cjakma/wood-case-keyboard/pics/IMG_2515.JPG

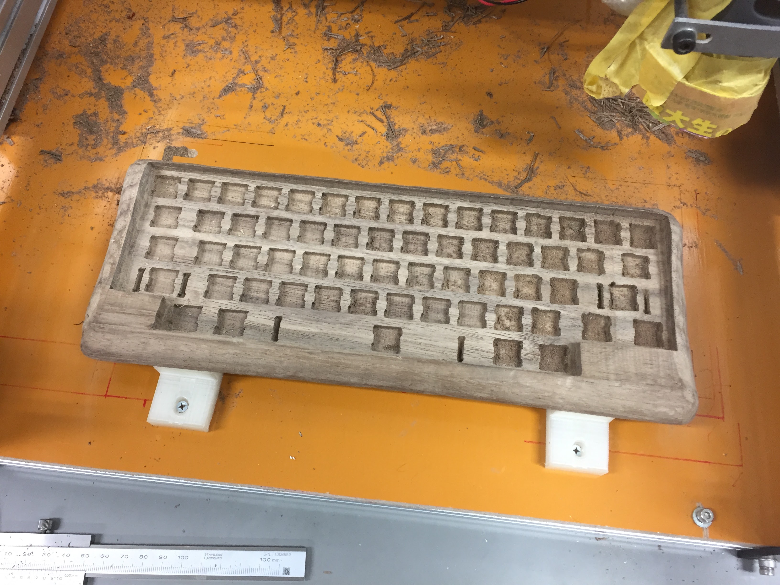
pics/IMG_2515.JPG
