cjakma/wood-case-keyboard/pics/IMG_2516.JPG

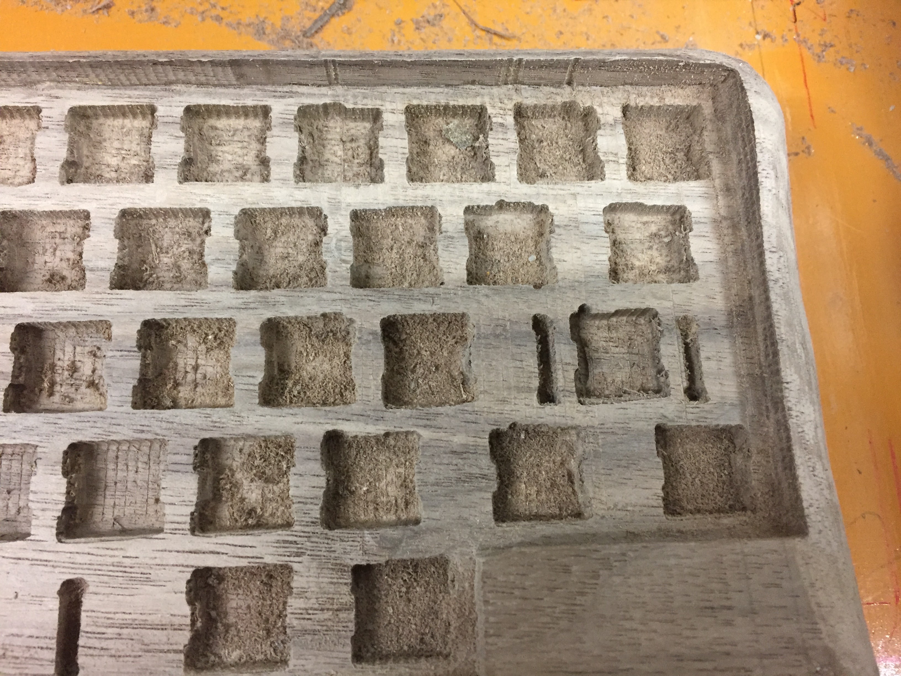
pics/IMG_2516.JPG
