cjakma/wood-case-keyboard/pics/IMG_2567.JPG

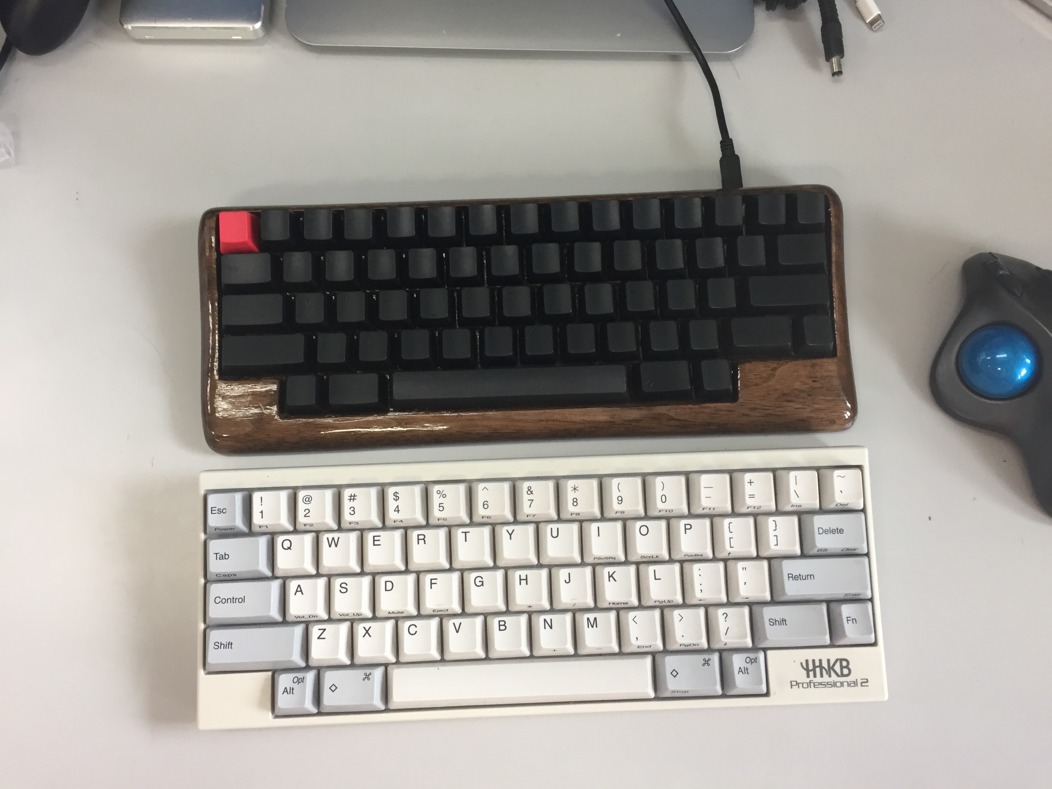
pics/IMG_2567.JPG
