cjakma/wood-case-keyboard/pics/IMG_2568.JPG

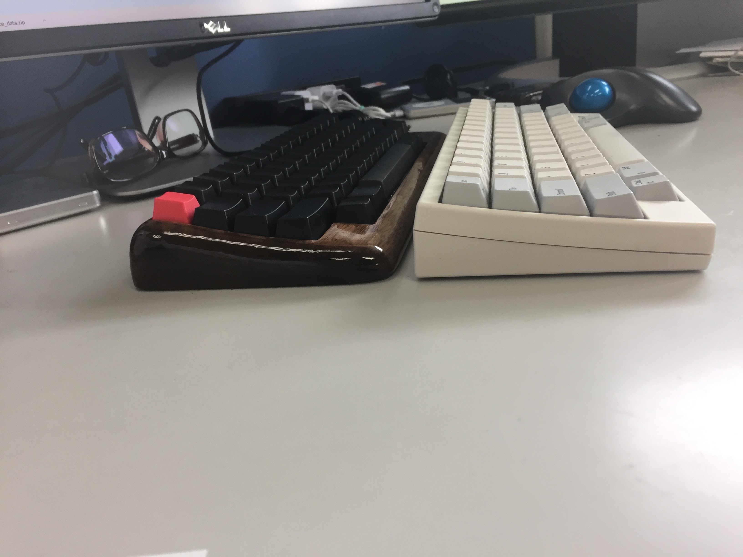
pics/IMG_2568.JPG
