cjakma/wood-case-keyboard/pics/IMG_2570.JPG

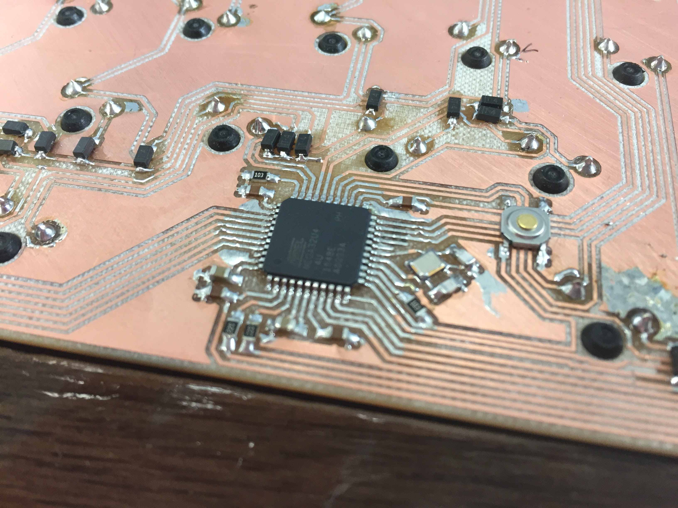
pics/IMG_2570.JPG
