cjakma/wood-case-keyboard/model/bottom_cutout.scad

use <scad-utils/morphology.scad>
include <common.scad>


invert_2D() bottom_cutout_2D();

/* bottom_cutout(); */
module bottom_cutout_2D()
{
    outset(r=0.5)
    square(plate_size);
}

module bottom_cutout()
{
    difference()
    {
        cube([plate_size()[0], plate_size()[1], block_height()]);

        translate((block_height()-lip_depth()-3.6)*z())
        linear_extrude(height=lip_depth()+3.6+0.1)
        bottom_cutout_2D();
    }
}
