cjakma/wood-case-keyboard/model/common.scad

include <params.scad>

inch = 25.4;
unit = 19.05;
x = [1, 0, 0];
y = [0, 1, 0];
z = [0, 0, 1];

// margin as 2D vector, to be added outside of the keyboard 
margin = [3, 2];

// tilt angle of the keyboard in degree unit
tilt = 10;

// ront_height height of the keyboard at front side. overall height will be
// calculated based on front_height and tilt_angle. make sure that there is
// enough room for PCB to be placed under the keyboard.
front_height = 14;

// roundnessness radius at side
roundness = 10;

// size of material to carve
block_size = [330, 130, 34];

// roundness of top of case
R = 400;

// maximum distance from top of your keyboard to switch mount surface.
lip_depth = 7.5;

// following are calcualted parameters
mx = margin[0];
my = margin[1];
px = plate_size[0];
py = plate_size[1];

h1 = front_height;
h2 = h1 + py*sin(tilt);
w = py*cos(tilt);

p = sq(h2-h1)/sq(w);
q = (sq(w)+sq(h2)-sq(h1))/(2*(h2-h1));
r = p+1;
s = -2*(p*q+h1);
t = p*sq(q)+sq(h1)-sq(R);
b = (-s+sqrt(sq(s)-4*r*t))/(2*r);
a = -sqrt(sq(R)-sq(h1-b));

o0 = 6;
o2 = 4;

function sq(x) = pow(x, 2);
function t1(x) = b - sqrt(sq(R) - sq(x-a))-roundness;
function t0(x) =
    let(b = my)
    let(a = d1(0) / (o0*pow(-b, o0-1)))
    let(c = t1(0) - a*pow(-b, o0))
    a*pow(x-b, o0)+c;
function t2(x) = 
    let(b = w+my)
    let(a = d1(w) / (o2*pow(w-b, o2-1)))
    let(c = t1(w) - a*pow(w-b, o2))
    a*pow(x-b, o2)+c;
function d1(x) = (x-a) / sqrt(sq(R) - sq(x-a));
function d0(x) = 
    let(b = my)
    let(a = d1(0) / (o0*pow(-b, o0-1)))
    let(c = t1(0) - a*pow(-b, o0))
    o0*a*pow(x-b, o0-1);
function d2(x) = 
    let(b = w+my)
    let(a = d1(w) / (o2*pow(w-b, o2-1)))
    let(c = t1(w) - a*pow(w-b, o2))
    o2*a*pow(x-b,o2-1);
function traj(x) =
    x <= 0 ? t0(x) :
    x <= w ? t1(x) : t2(x);
function devi(x) = 
    x <= 0 ? d0(x) :
    x <= w ? d1(x) : d2(x);
function ymin() = 
    let(b = my)
    let(a = d1(0) / (o0*pow(-b, o0-1)))
    let(c = t1(0) - a*pow(-b, o0))
    -abs(pow(-c/a, 1/o0))+b-roundness;
function ymax() =
    let(b = w+my)
    let(a = d1(w) / (o2*pow(w-b, o2-1)))
    let(c = t1(w) - a*pow(w-b, o2))
    abs(pow(-c/a, 1/o2))+b+roundness;
function xmin() = -mx-roundness;
function xmax() = px+mx+roundness;
function base_size() = [xmax()-xmin(), ymax()-ymin(), block_size[2]];
function block_height() = block_size[2];
function tilted_height() = front_height + (ymax()-ymin())*sin(tilt);

half_circle = [for (i = [0 : 180/12 : 180]) [cos(i), sin(i)]];

module invert_2D()
{
    difference() {
        translate([xmin(), ymin()]) square([block_size[0], block_size[1]]);
        children();
    }
}

module mirrored(d) {
    children();
    mirror(d) children();
}
